Alan-Lomax/Power_Pickup_Whisker_Probe/Documentation/Photos/Figure 3 Single PCB with Diode in Place.jpg

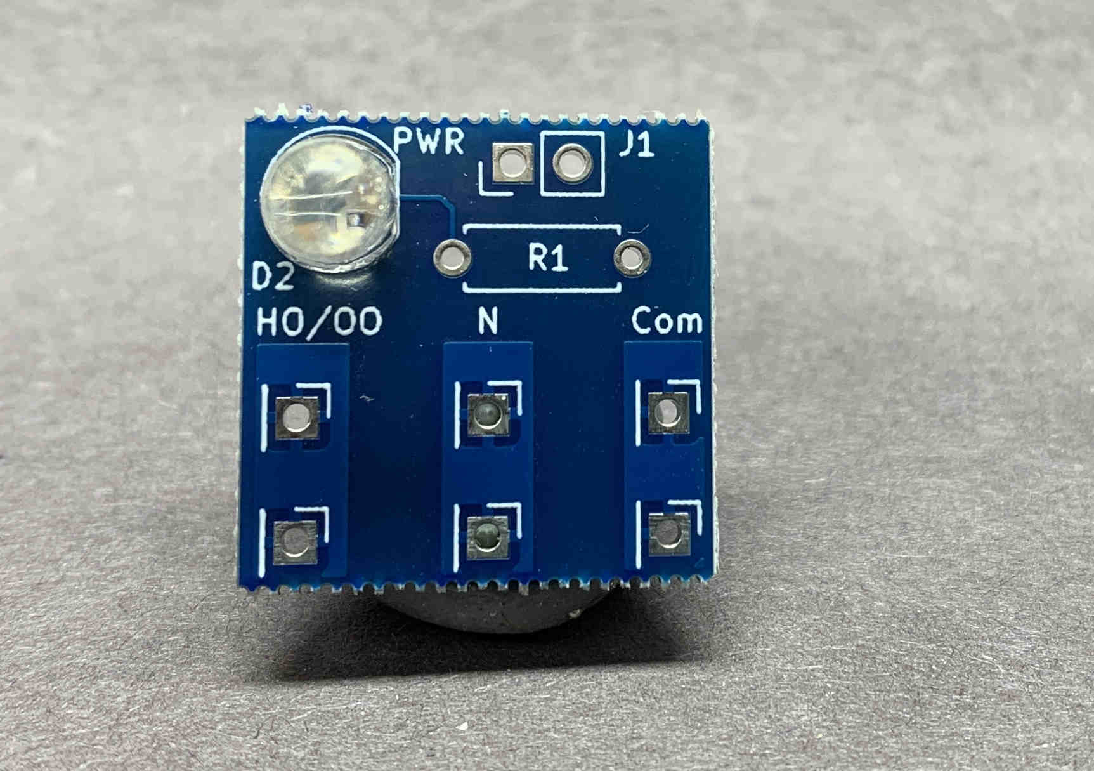
Documentation/Photos/Figure 3 Single PCB with Diode in Place.jpg
