Alan-Lomax/Power_Pickup_Whisker_Probe/Documentation/Photos/Figure 5 LED leads and Mouse Bites.jpg

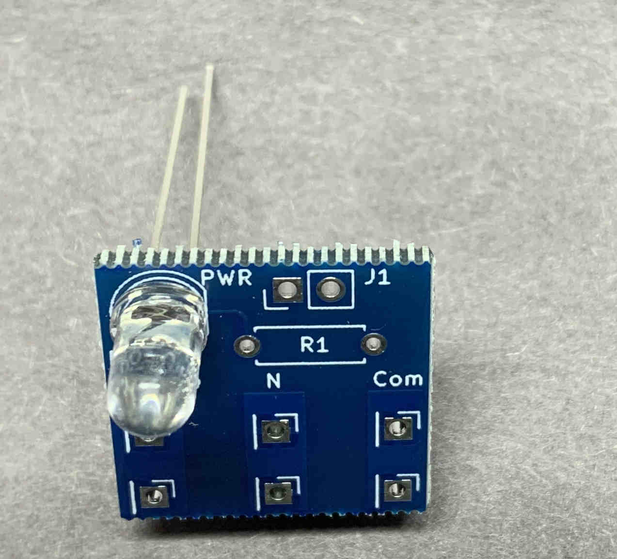
Documentation/Photos/Figure 5 LED leads and Mouse Bites.jpg
