Alan-Lomax/Power_Pickup_Whisker_Probe/Documentation/Photos/Figure 9 Finished Product.jpg

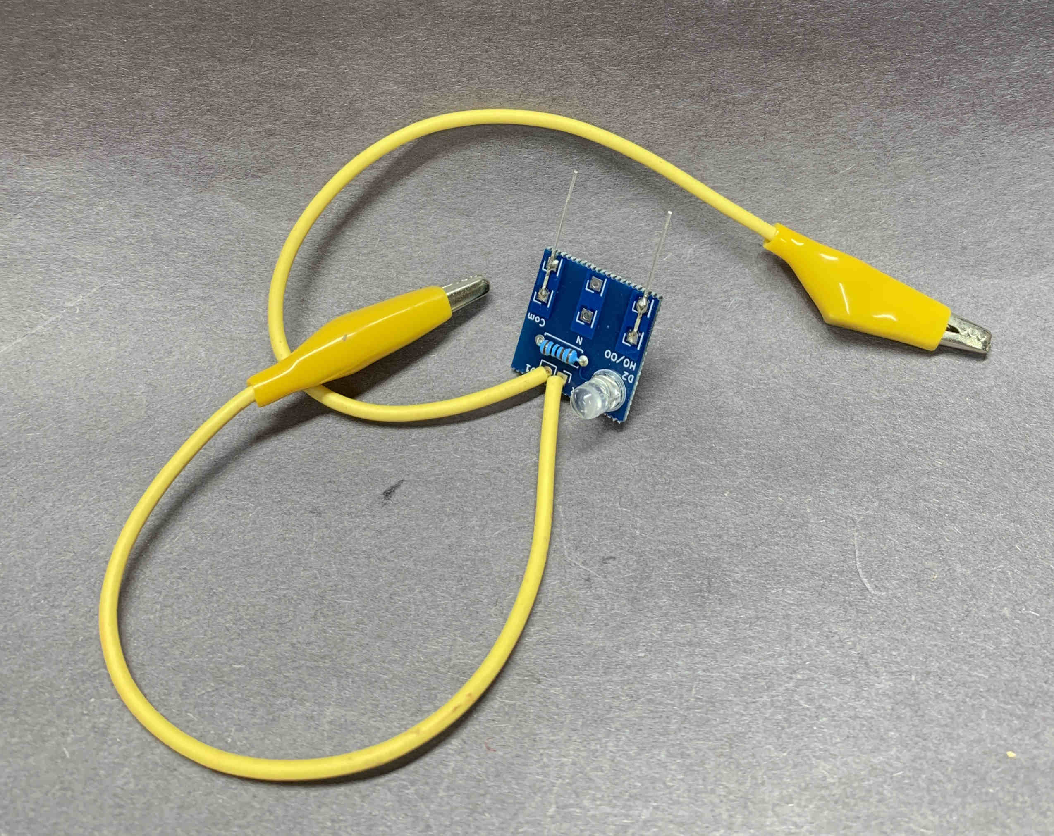
Documentation/Photos/Figure 9 Finished Product.jpg
