Alan-Lomax/Power_Pickup_Whisker_Probe/Documentation/Photos/Figure 10a - Track Power via Whiskers.jpg

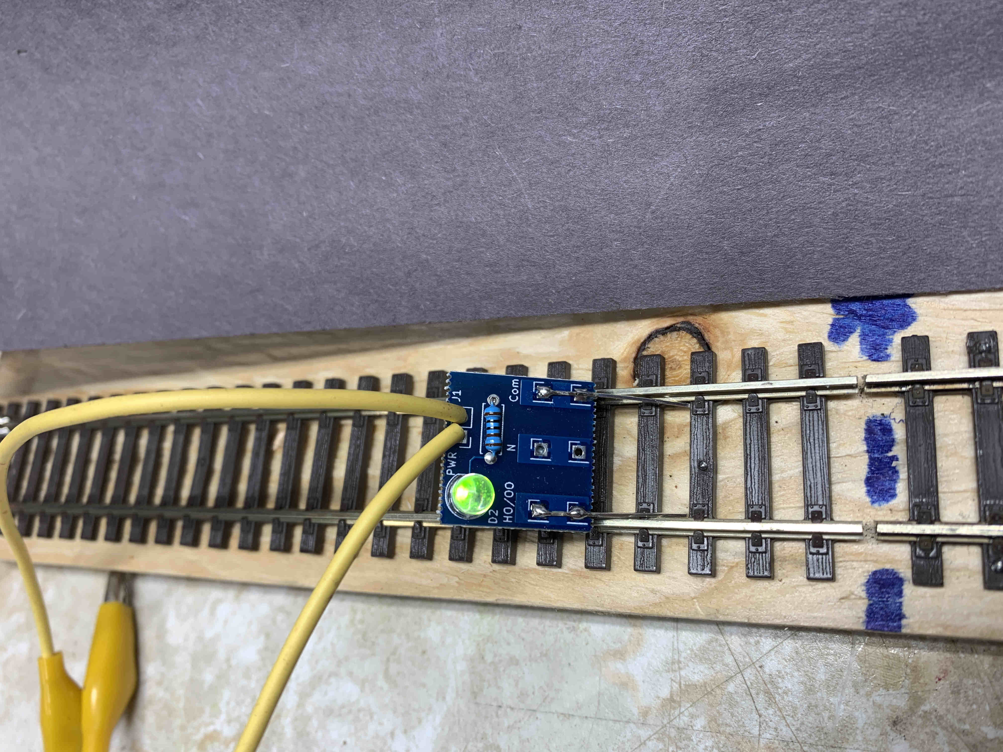
Documentation/Photos/Figure 10a - Track Power via Whiskers.jpg
