Alan-Lomax/Power_Pickup_Whisker_Probe/Documentation/Photos/Figure 10b - Track Power.jpg

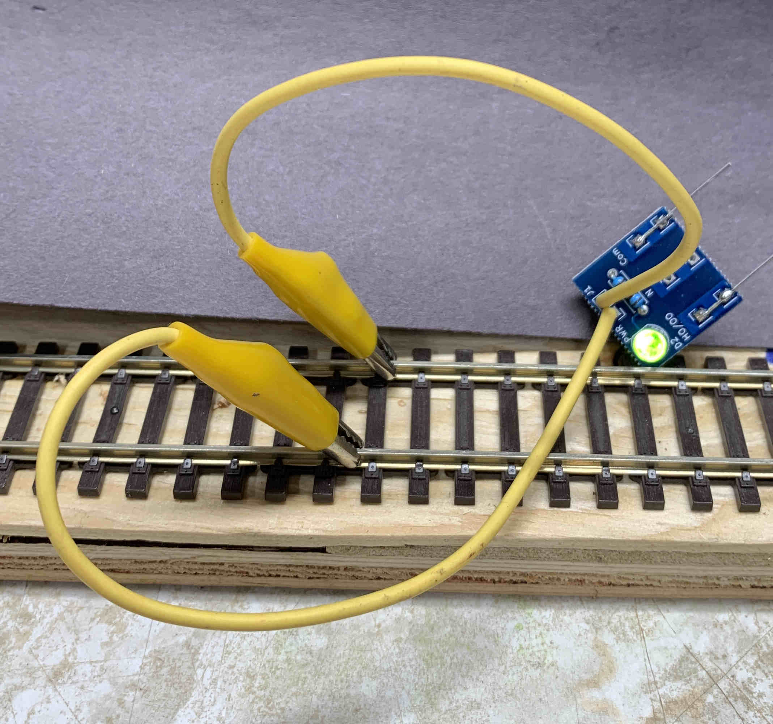
Documentation/Photos/Figure 10b - Track Power.jpg
