Alan-Lomax/Power_Pickup_Whisker_Probe/Documentation/Photos/Figure 10d - Track Power via PCB only.jpg

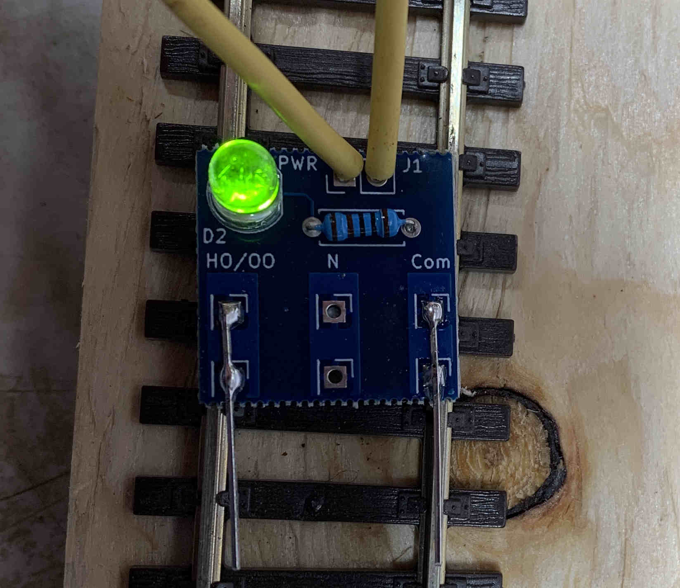
Documentation/Photos/Figure 10d - Track Power via PCB only.jpg
