Alan-Lomax/Power_Pickup_Whisker_Probe/Documentation/Photos/Figure 3 Parts.jpg

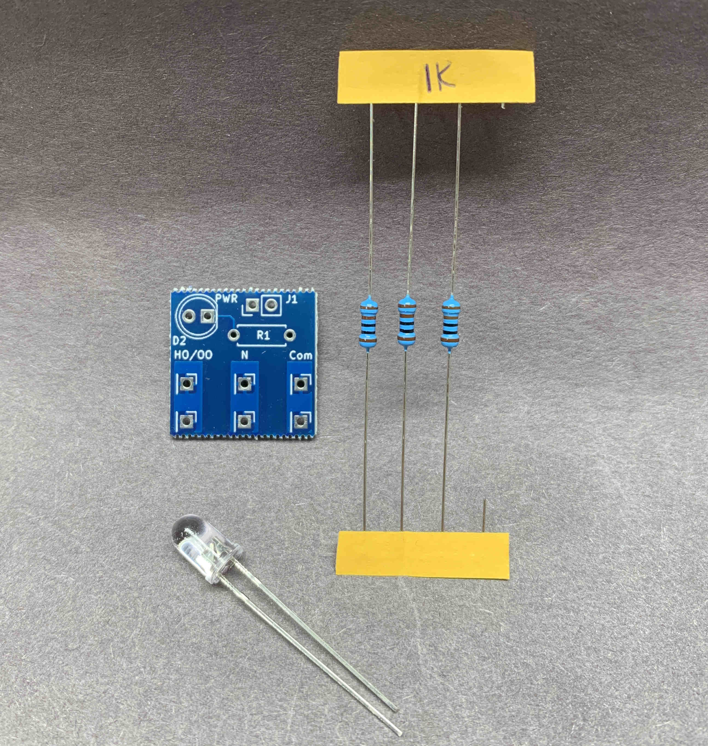
Documentation/Photos/Figure 3 Parts.jpg
