Alan-Lomax/Power_Pickup_Whisker_Probe/Documentation/Photos/Figure 7 Installing leads and Resistor in Place.jpg

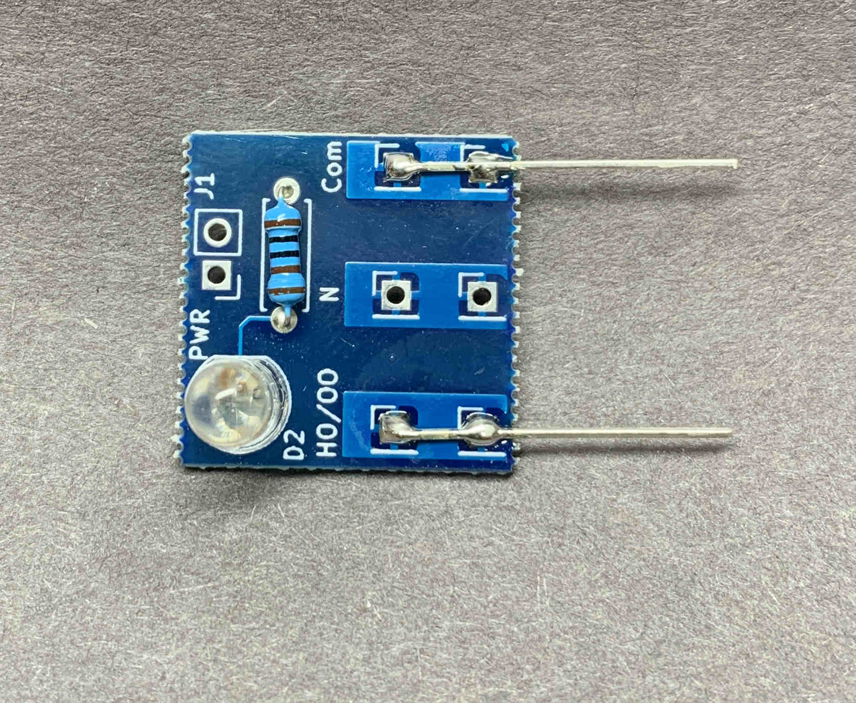
Documentation/Photos/Figure 7 Installing leads and Resistor in Place.jpg
